mjongerh/KrangleBoard/STLfiles/STL_parts/Bracket_teensy2++_add1.stl

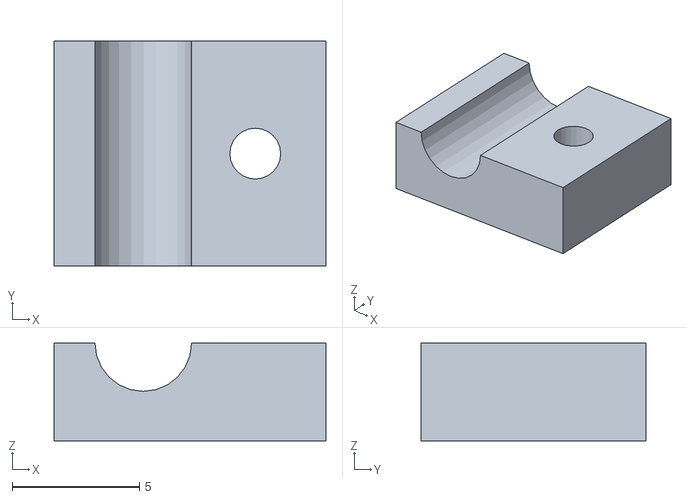
[picture p28: CAD file, 2022-02-26]
STLfiles/STL_parts/Bracket_teensy2++_add1.stl
10.7 x 8.85 x 3.85
