mjongerh/KrangleBoard/STLfiles/STL_parts/BaseplateA5.stl

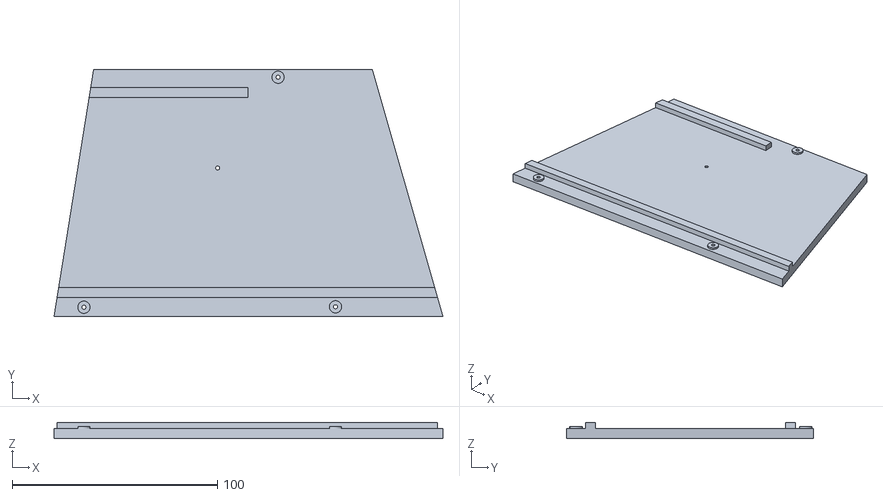
[picture p29: CAD file, 2022-02-26]
STLfiles/STL_parts/BaseplateA5.stl
189.4 x 120.2 x 8.00
