mjongerh/KrangleBoard/STLfiles/STL_parts/Bracket_teensy2++_add2.stl

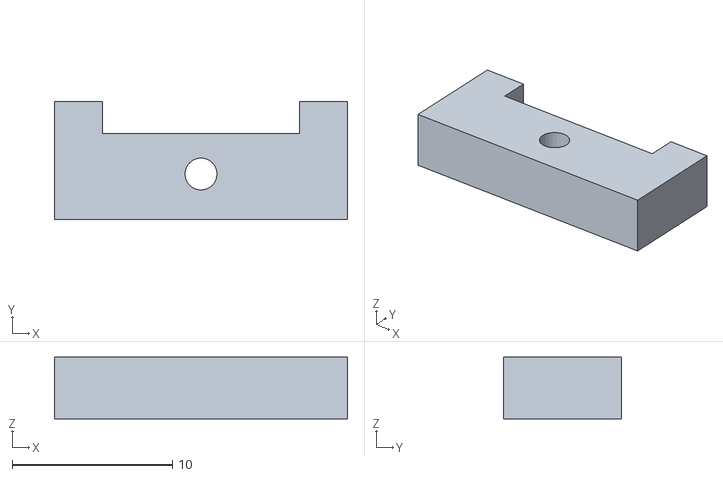
[picture p30: CAD file, 2022-02-26]
STLfiles/STL_parts/Bracket_teensy2++_add2.stl
18.3 x 7.40 x 3.85
