mjongerh/KrangleBoard/STLfiles/STL_parts/TopplateC3.stl

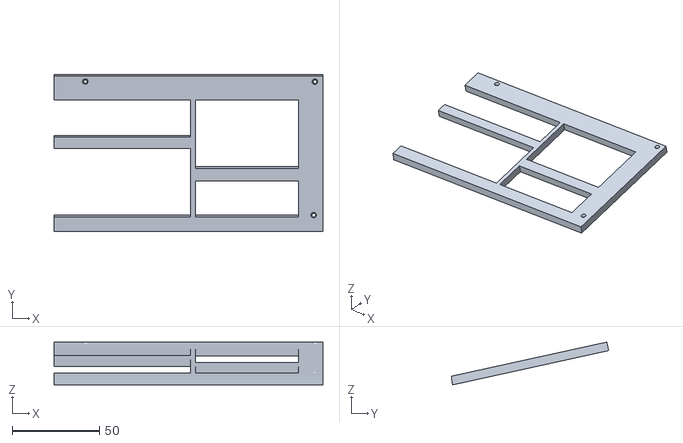
[picture p31: CAD file, 2022-02-26]
STLfiles/STL_parts/TopplateC3.stl
154.1 x 90.2 x 24.5
