mjongerh/KrangleBoard/STLfiles/STL_parts/BaseplateA3.stl

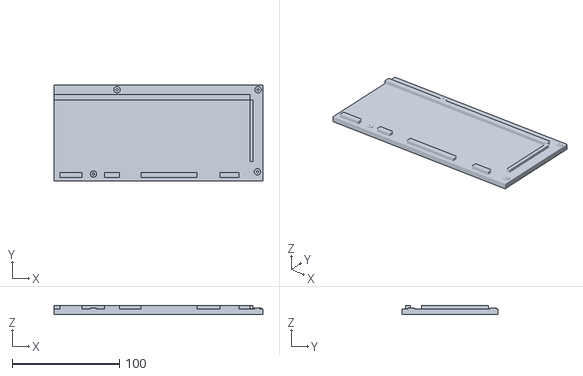
[picture p32: CAD file, 2022-02-26]
STLfiles/STL_parts/BaseplateA3.stl
194.9 x 89.7 x 8.00
