mjongerh/KrangleBoard/STLfiles/STL_parts/SwitchplateB1.stl

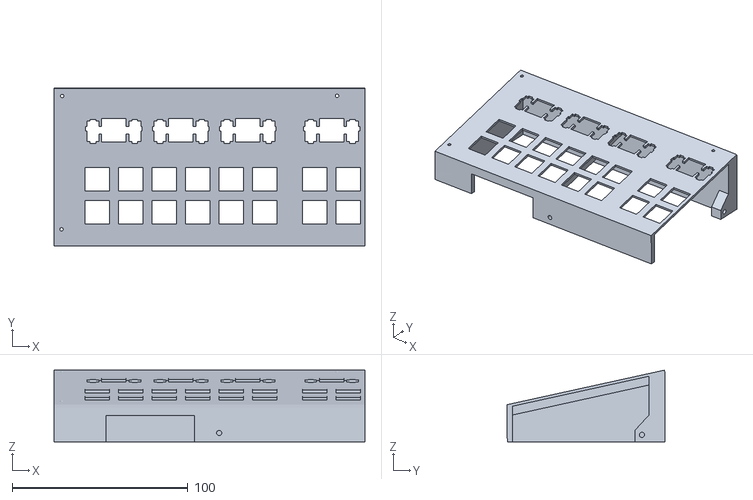
[picture p33: CAD file, 2022-02-26]
STLfiles/STL_parts/SwitchplateB1.stl
176.8 x 89.9 x 40.8
