mjongerh/KrangleBoard/STLfiles/STL_parts/BaseplateA2.stl

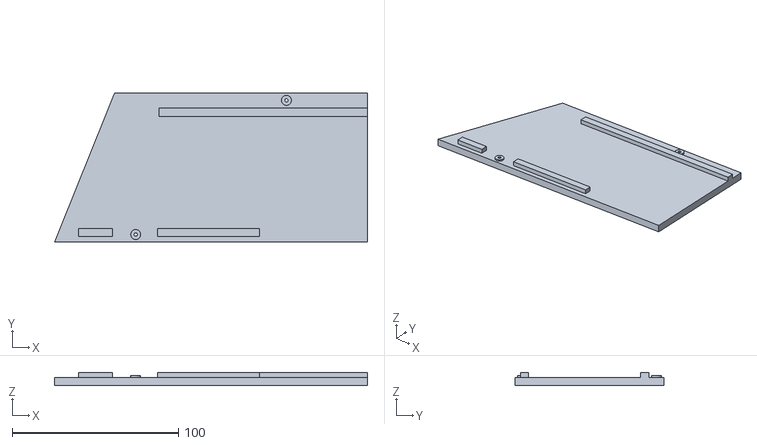
[picture p34: CAD file, 2022-02-26]
STLfiles/STL_parts/BaseplateA2.stl
188.1 x 89.7 x 8.00
