mjongerh/KrangleBoard/STLfiles/STL_parts/TopplateC2.stl

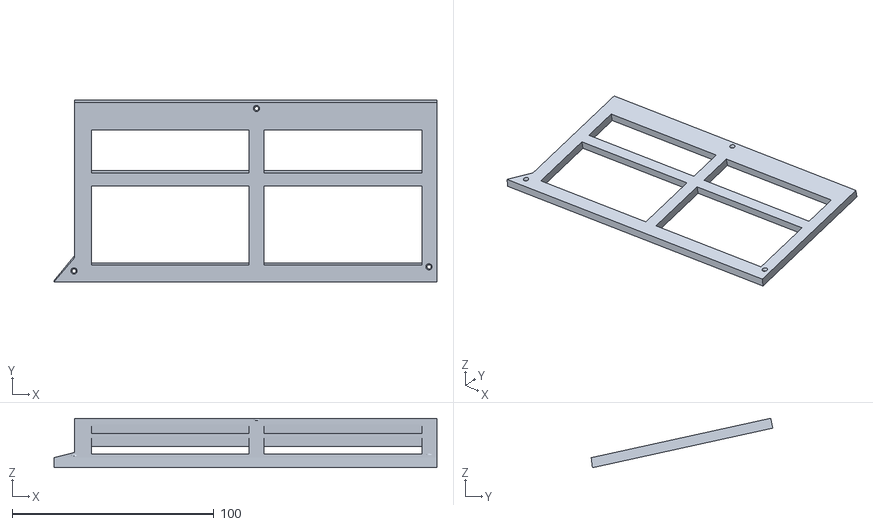
[picture p35: CAD file, 2022-02-26]
STLfiles/STL_parts/TopplateC2.stl
190.1 x 90.2 x 24.5
