mjongerh/KrangleBoard/STLfiles/STL_parts/BaseplateA1.stl

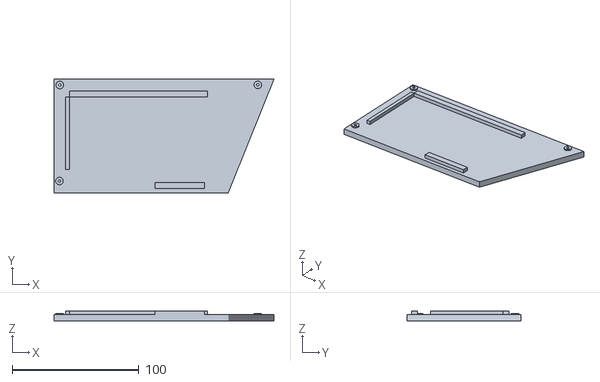
[picture p36: CAD file, 2022-02-26]
STLfiles/STL_parts/BaseplateA1.stl
173.7 x 89.7 x 8.00
